dkorobkov/Mega8And7SegLed/solder_bottom_2led.png

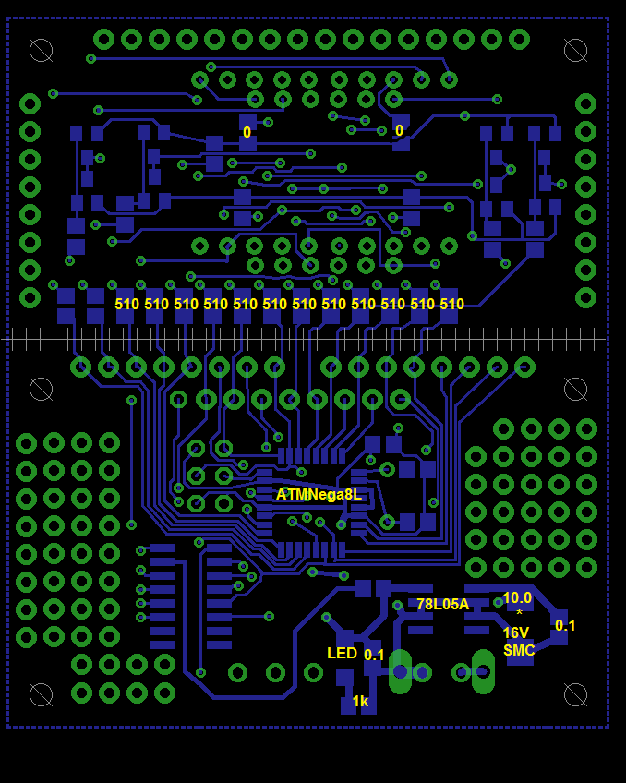
solder_bottom_2led.png
